Upani-Gunathunga/Oscivox-Analog-Acoustic-Guitar-Tuner-EN2091-Analog-Project/SimulationFiles/Bandpass for E4.asc

C1: cap; 47n
C2: cap; 47n
R1: res; 60k
R2: res; 10.272k
R3: res; 10.272k
R4: res; 10.272k
R5: res; 10.272k
R6: res; 10.272k
R7: res; 10.272k
R8: res; 700k
U1: opamp2; TL072
U2: opamp2; TL072
U3: opamp2; TL072
U4: opamp2; TL072
V1: voltage; ""; AC 1
V2: voltage; 15
V3: voltage; -15
Named nets: 0
.ac oct 100 1 1k
Output
Input
.lib TL072.lib
