Upani-Gunathunga/Oscivox-Analog-Acoustic-Guitar-Tuner-EN2091-Analog-Project/SimulationFiles/16_Oscivox_EN2091_LTspice Simulations/ADP.asc

B1: bv; V=white(100000*time)/1000
C1: cap; 0.64µ
C2: cap; 12µ
C3: cap; 125µ
C4: cap; 270nf
Q1: npn
R1: res; 100
R2: res; 100
R3: res; 100
R4: res; 100
R5: res; 100
R6: res; 100
R7: res; 100
R8: res; 1k
R9: res; 1k
R10: res; 10
R11: res; 1.2k
R12: res; 20k
R13: res; 4k
R14: res; 330
R15: res; 1k
R16: res; 800
R17: res; 1k
R18: res; 100k
U1: opamp
U2: LT1115
V1: voltage; SINE(0 1m 82.41)
V2: voltage; SINE(0 1m 110)
V3: voltage; SINE(0 1m 146.83)
V4: voltage; SINE(0 1m 196)
V5: voltage; SINE(0 1m 246.94)
V6: voltage; SINE(0 1m 329.63)
V7: voltage; 7v
V8: voltage; 7
V9: voltage; 7
Named nets: 0, noice, signal, outpre, +5, -5, out
.tran 10m
.lib opamp.sub
I/P L R
i/p resister safe zone to handle 1mv input
I/P R
.MODEL BC549B NPN(IS=4.679E-14 ISE=2.642f ISC=2.337E-14 XTI=3 BF=458.7 BR=11.57 IKF=0.1371 IKR=0.1144 XTB=1.5 VAF=52.64 VAR=364.5 VJE=0.5591 VJC=0.1994 RE=0.2598 RC=1 RB=1 RBM=1 IRB=1E-06 CJE=1.229E-11 CJC=4.42p XCJC=0.6193 FC=0.7936 NF=1.01 NR=1.019 NE=1.581 NC=1.164 MJE=0.3385 MJC=0.2782 TF=4.689E-10 TR=1m2 ITF=0.8842 VTF=2.828 XTF=160 EG=1.11 VCEO=30 ICRATING=100m MFG=PHILIPS)
.inc opa1656.lib
.include OPA1656.lib
